AntonioMR/Nano-Play-Board/Imagenes/Completa_cara_superior.png

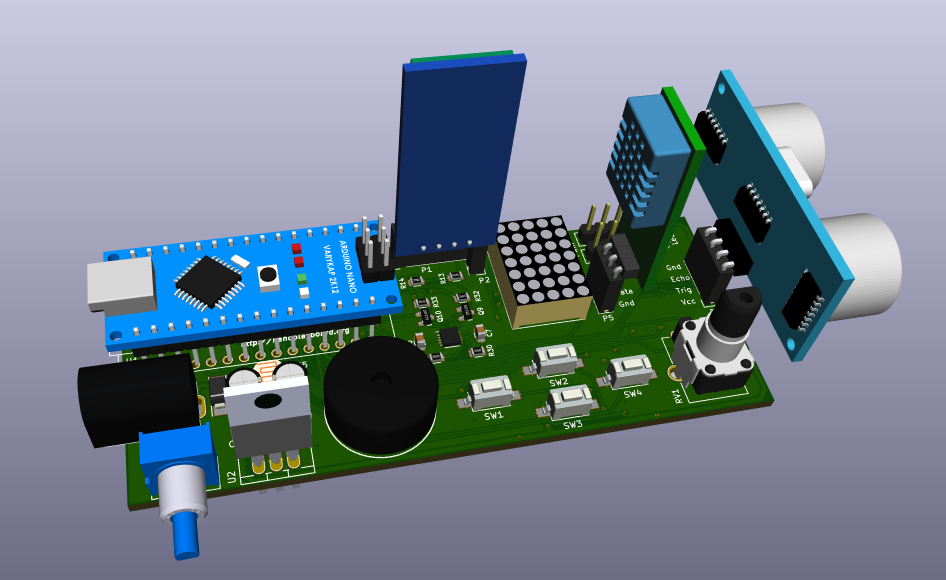
Imagenes/Completa_cara_superior.png
