AntonioMR/Nano-Play-Board/Imagenes/dht11_pins.png

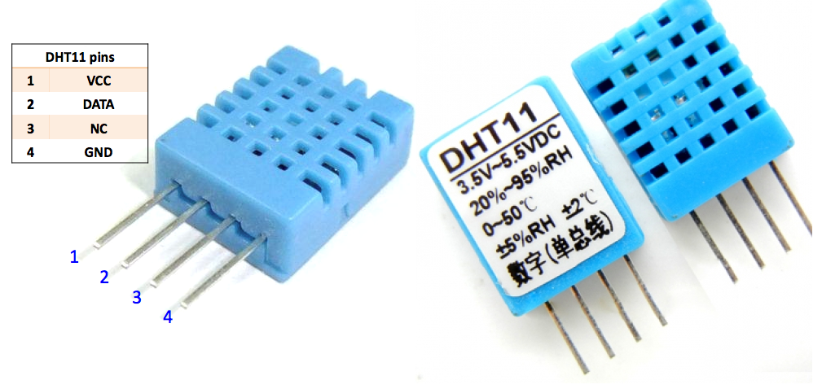
Imagenes/dht11_pins.png
