AntonioMR/Nano-Play-Board/Imagenes/encoder.jpg

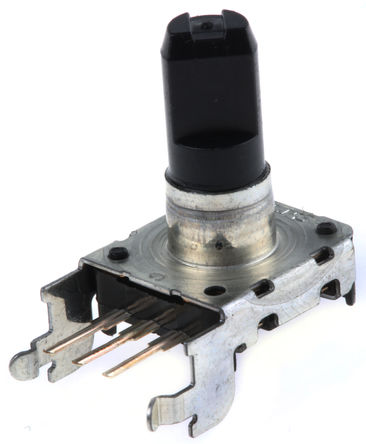
Imagenes/encoder.jpg
