AntonioMR/Nano-Play-Board/Imagenes/esp8266.jpg

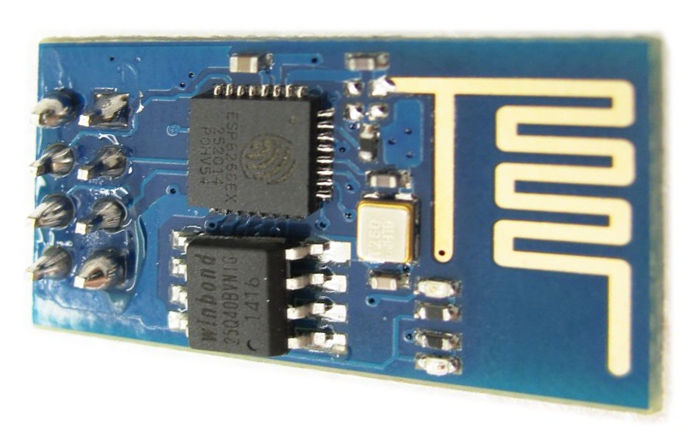
Imagenes/esp8266.jpg
