AntonioMR/Nano-Play-Board/Imagenes/HC_05_BT.jpg

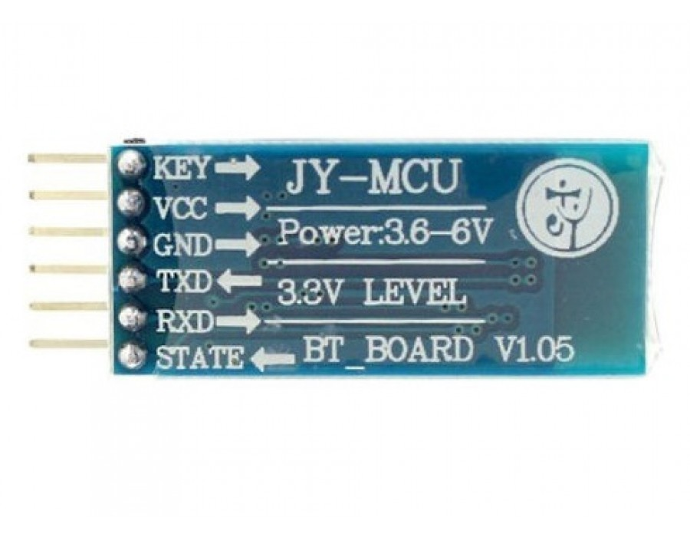
Imagenes/HC_05_BT.jpg
