AntonioMR/Nano-Play-Board/Imagenes/ldr.jpg

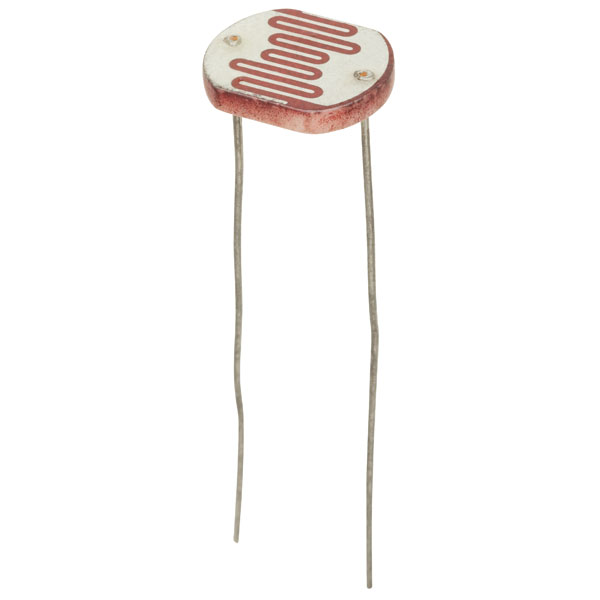
Imagenes/ldr.jpg
