AntonioMR/Nano-Play-Board/Imagenes/MatrizLed.jpg

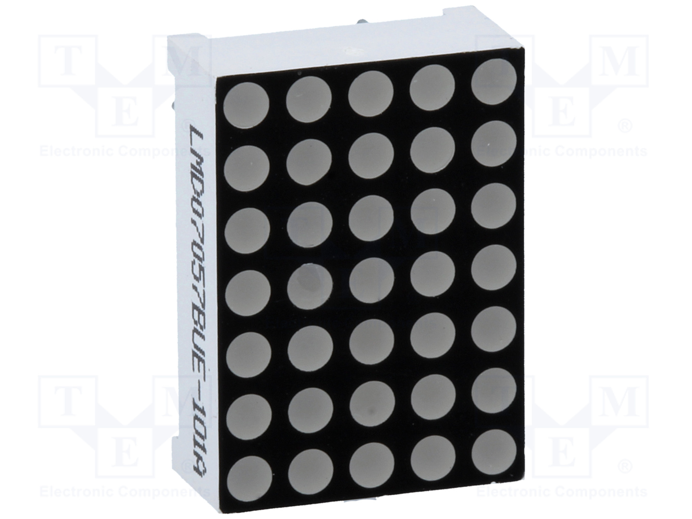
Imagenes/MatrizLed.jpg
