AntonioMR/Nano-Play-Board/Imagenes/PCB_cara_inferior.png

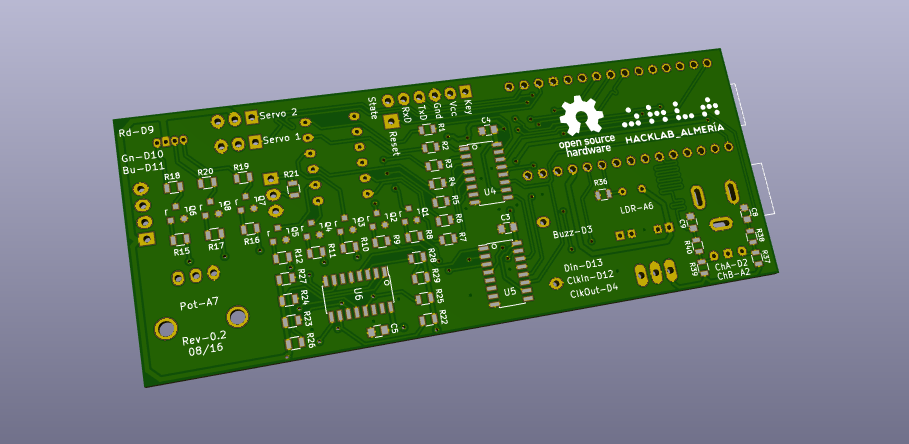
Imagenes/PCB_cara_inferior.png
