AntonioMR/Nano-Play-Board/Imagenes/PCB_cara_superior.png

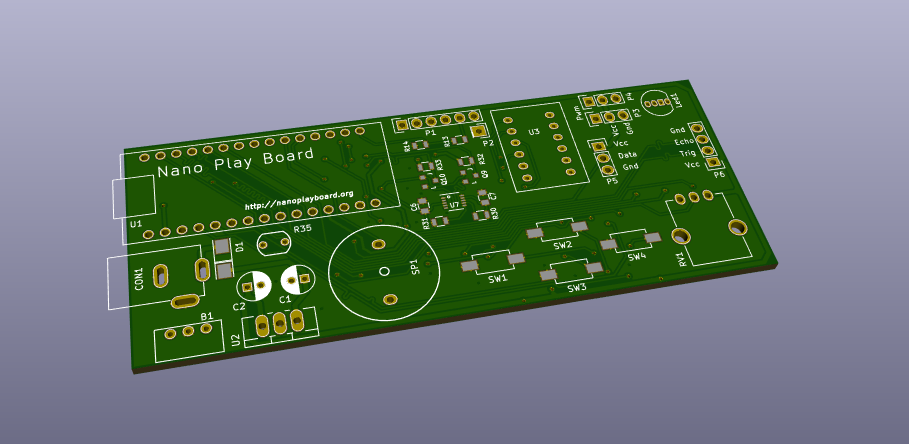
Imagenes/PCB_cara_superior.png
